emb3rcia/spark-switch/Firmware/ethernet_switch/Core/Src/webui.h

//
// Created by ember on 2/28/26.
//

#ifndef ETHERNET_SWITCH_WEBUI_H
#define ETHERNET_SWITCH_WEBUI_H

#include "main.h"

void StartWebUITask(void const * argument);

#endif //ETHERNET_SWITCH_WEBUI_H
